ayachaieb/smart-hydroponic-system-project/mechanic design of hydroponic system/the_nft_design/front wall.SLDPRT

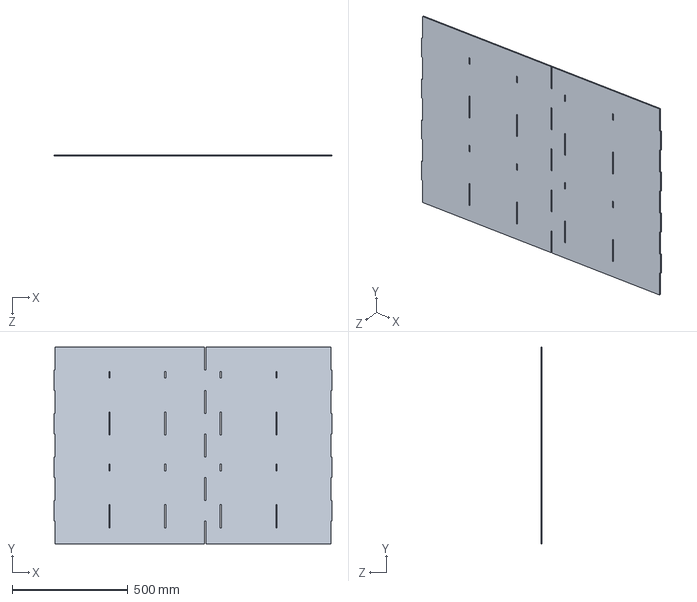
[picture p16: CAD file, 2024-11-08]
mechanic design of hydroponic system/the_nft_design/front wall.SLDPRT
1200.0 x 850.0 x 5.00 mm
