ayachaieb/smart-hydroponic-system-project/mechanic design of hydroponic system/the_nft_design/plant.SLDPRT

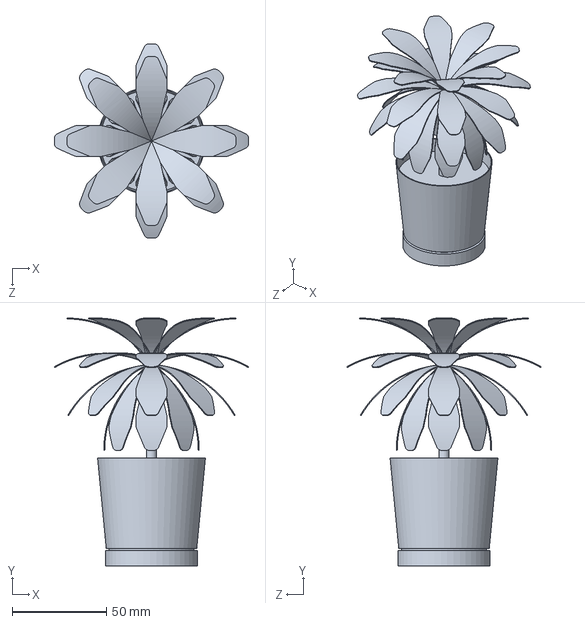
[picture p17: CAD file, 2024-11-08]
mechanic design of hydroponic system/the_nft_design/plant.SLDPRT
103.3 x 131.7 x 103.3 mm
