ayachaieb/smart-hydroponic-system-project/mechanic design of hydroponic system/the_nft_design/base.SLDPRT

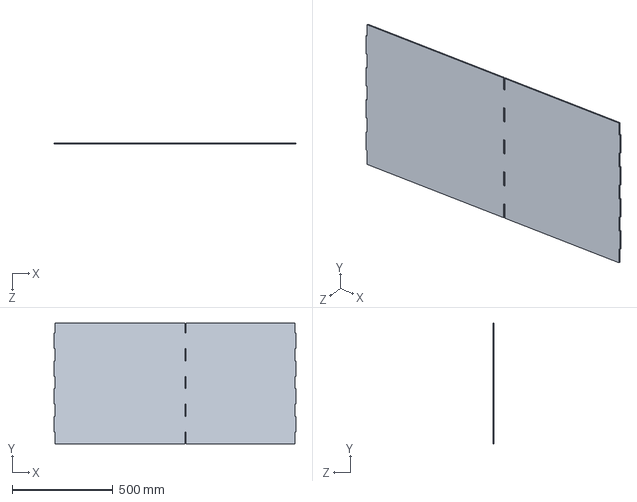
[picture p18: CAD file, 2024-11-08]
mechanic design of hydroponic system/the_nft_design/base.SLDPRT
1200.0 x 600.0 x 5.00 mm
